specs32/specs_keys/gh80-3003-nicosmod/gh80-3003-nicosmod.kicad_sch

## KiCad design gh80-3003-nicosmod/gh80-3003-nicosmod.kicad_sch (2021-04-06)

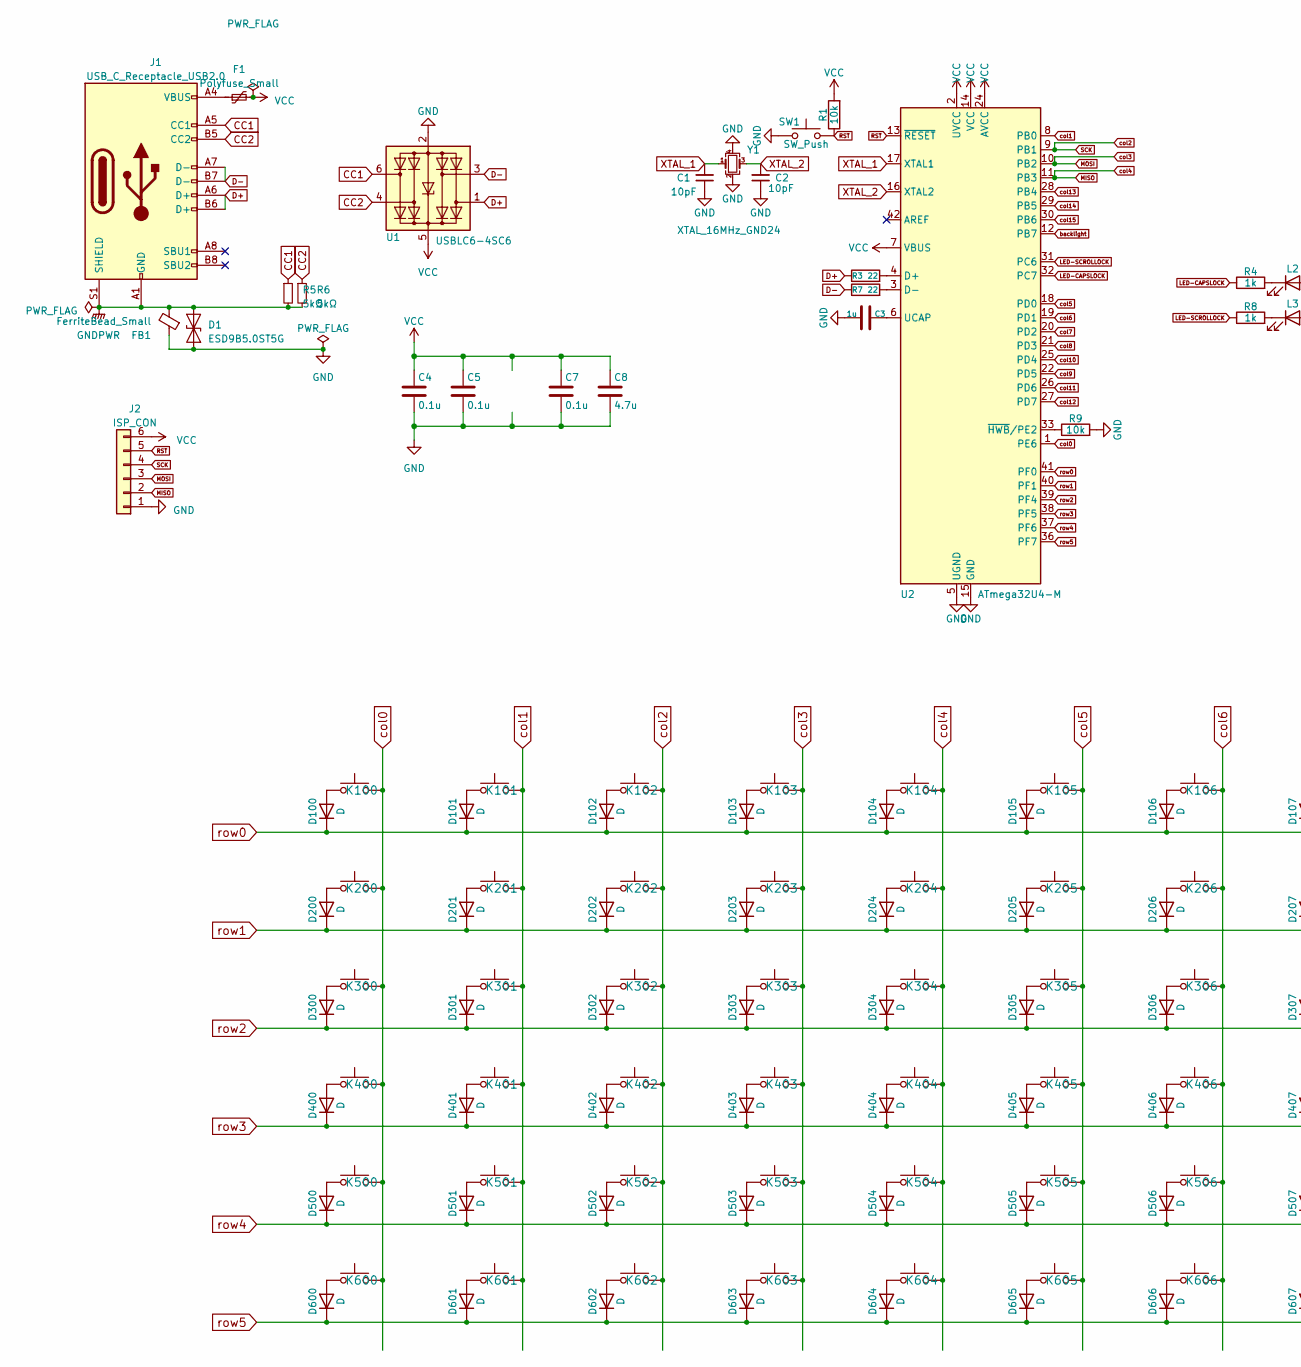
[picture p9: schematic gh80-3003-nicosmod.kicad_sch, part in row 1, column 1]

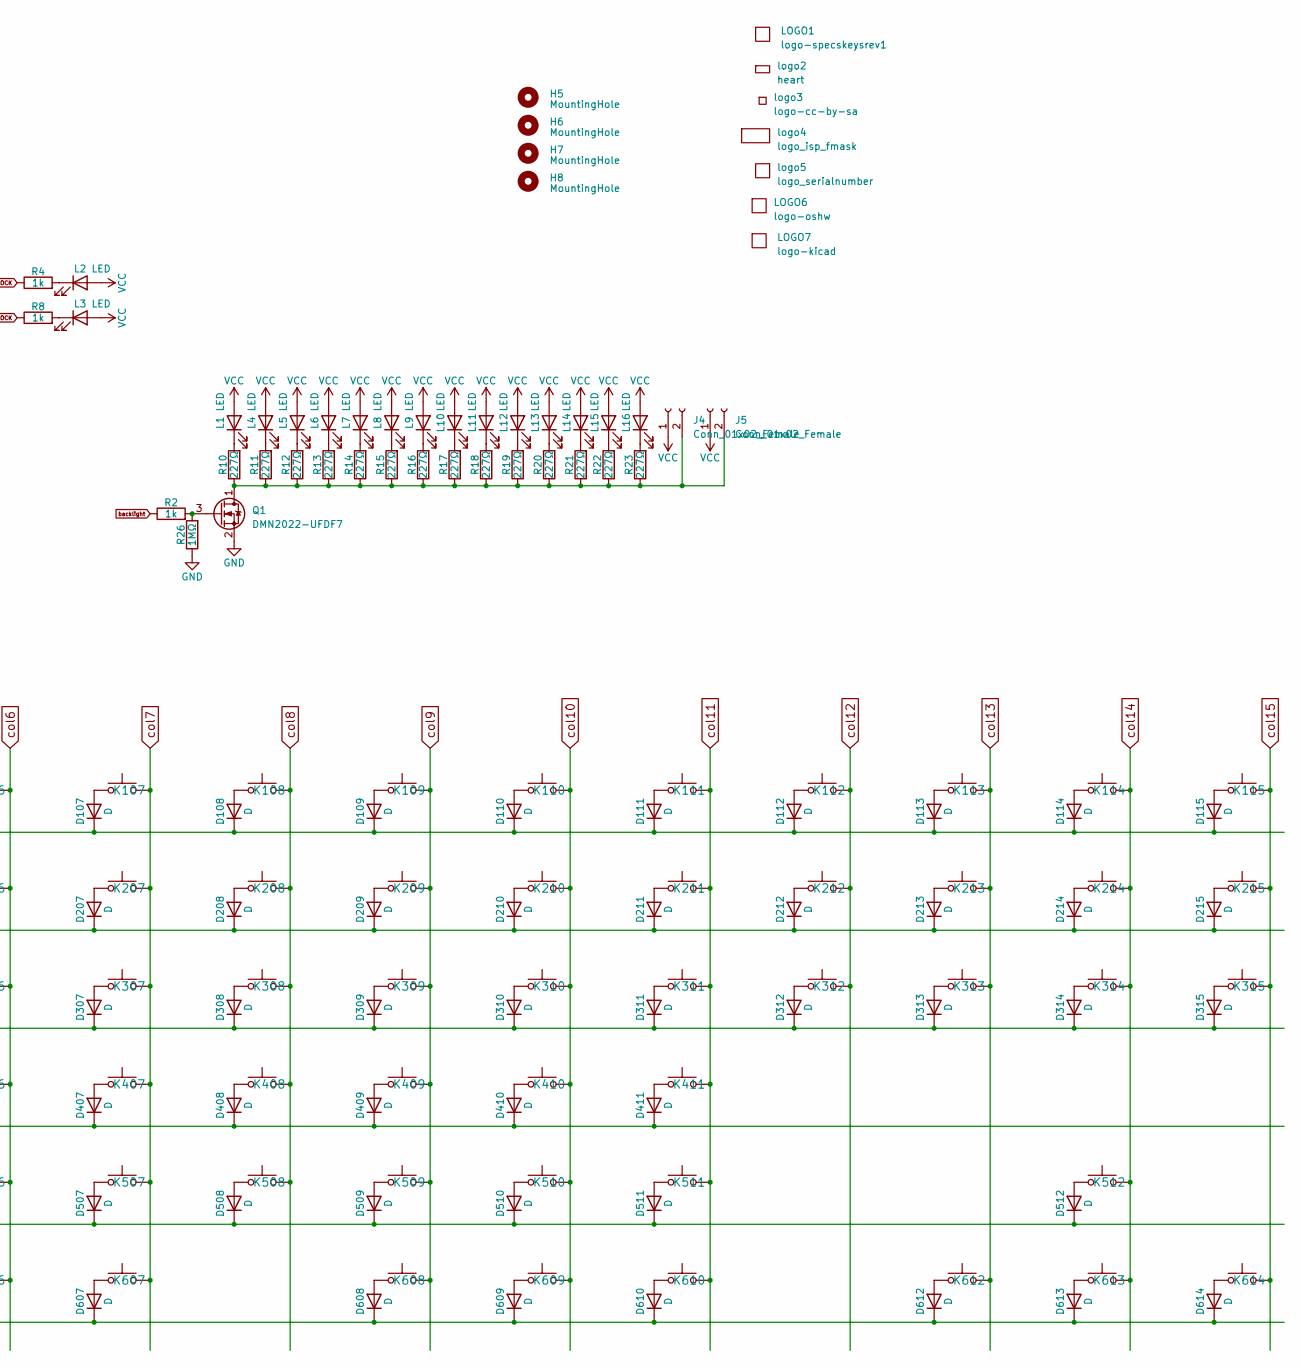
[picture p10: schematic gh80-3003-nicosmod.kicad_sch, part in row 1, column 2]

Parts:
C1, C2: 10pF; C_0603_1608Metric_Pad1.08x0.95mm_HandSolder
C3: 1u; C_0805_2012Metric_Pad1.18x1.45mm_HandSolder
C4, C5, C7: 0.1u; C_0603_1608Metric
C8: 4.7u; C_0805_2012Metric_Pad1.18x1.45mm_HandSolder
D1: ESD9B5.0ST5G; D_0402_1005Metric_Pad0.77x0.64mm_HandSolder
D100, D101, D102, D103, D104, D105, D106, D107, D108, D109, D110, D111, D112, D113, D114, D115, D200, D201, D202, D203, D204, D205, D206, D207, D208, D209, D210, D211, D212, D213, D214, D215, D300, D301, D302, D303, D304, D305, D306, D307, D308, D309, D310, D311, D312, D313, D314, D315, D400, D401, D402, D403, D404, D405, D406, D407, D408, D409, D410, D411, D500, D501, D502, D503, D504, D505, D506, D507, D508, D509, D510, D511, D512, D600, D601, D602, D603, D604, D605, D606, D607, D608, D609, D610, D612, D613, D614: D; D_0402_1005Metric_Pad0.77x0.64mm_HandSolder
F1: Polyfuse_Small; R_0805_2012Metric_Pad1.20x1.40mm_HandSolder
FB1: FerriteBead_Small; R_0805_2012Metric_Pad1.20x1.40mm_HandSolder
H5, H6, H7, H8: MountingHole; MountingHole_4mm
J1: USB_C_Receptacle_USB2.0; USB_C_Receptacle_JAE_DX07S016JA1R1500
J2: ISP_CON; Conn_01x06_SMD_2mm
J4, J5: Conn_01x02_Female; PinHeader_1x02_P2.00mm_Vertical
K100, K101, K102, K103, K104, K105, K106, K107, K108, K109, K110, K111, K112, K113, K114, K115, K200, K201, K202, K203, K204, K205, K206, K207, K208, K209, K210, K211, K213, K214, K215, K300, K301, K302, K303, K304, K305, K306, K307, K308, K309, K310, K311, K313, K314, K315, K400, K401, K402, K403, K404, K405, K406, K407, K408, K409, K410, K411, K500, K501, K502, K503, K504, K505, K506, K507, K508, K509, K510, K512, K600, K605, K609, K612, K613, K614: SW_Push; SW_Cherry_MX_1.00u_PCB
K212: SW_Push; SW_Cherry_MX_2.00u_PCB
K312: SW_Push; SW_Cherry_MX_ISOEnter_PCB
K511: SW_Push; SW_Cherry_MX_2.75u_PCB
K601, K604, K606, K608, K610: SW_Push; SW_Cherry_MX_1.50u_PCB
K602: SW_Push; SW_Cherry_MX_1.75u_PCB
K603: SW_Push; SW_Cherry_MX_1.25u_PCB
K607: SW_Push; SW_Cherry_MX_7.00u_PCB
L1, L2, L3, L4, L5, L6, L7, L8, L9, L10, L11, L12, L13, L14, L15, L16: LED; LED_0805_2012Metric_Pad1.15x1.40mm_HandSolder
LOGO1: logo-specskeysrev1; logo_specskeysrev1
LOGO6: logo-oshw; OSHW-Symbol_6.7x6mm_Copper
LOGO7: logo-kicad; KiCad-Logo2_5mm_Copper
Q1: DMN2022-UFDF7; U-DFN2020-6 (Type F)
R1, R9: 10k; R_0603_1608Metric
R2, R4, R8: 1k; R_0603_1608Metric
R3, R7: 22; R_0603_1608Metric
R5, R6: 5kΩ; R_0603_1608Metric
R10, R11, R12, R13, R14, R15, R16, R17, R18, R19, R20, R21, R22, R23: 227Ω; R_0805_2012Metric
R26: 1MΩ; R_0603_1608Metric
SW1: SW_Push; SW_SPST_TL3342
U1: USBLC6-4SC6; SOT-23-6
U2: ATmega32U4-M; QFN-44-1EP_7x7mm_P0.5mm_EP5.2x5.2mm_ThermalVias
Y1: XTAL_16MHz_GND24; Crystal_SMD_2016-4Pin_2.0x1.6mm
logo2: heart; logo_heart3
logo3: logo-cc-by-sa; cc-by-sa
logo4: logo_isp_fmask; ISP_AT32
logo5: logo_serialnumber; JLC-SERIAL

Connections:
CC1: J1.A5 (CC1), R5.1, U1.6 (I/O4)
CC2: J1.B5 (CC2), R6.1, U1.4 (I/O3)
D+: J1.A6 (D+), J1.B6 (D+), R3.1, U1.1 (I/O1)
D-: J1.A7 (D-), J1.B7 (D-), R7.1, U1.3 (I/O2)
GND: C1.1, C2.1, C3.2, C4.2, C5.2, C7.2, C8.2, D1.1 (A1), FB1.1, J2.1, Q1.2 (S), R9.2, R26.1, SW1.1, U1.2 (GND), U2.5 (UGND), U2.15 (GND), U2.23 (GND), U2.35 (GND), U2.43 (GND), U2.45 (GND), Y1.2, Y1.4
GNDPWR: D1.2 (A2), FB1.2, J1.A1 (GND), J1.A12 (GND), J1.B1 (GND), J1.B12 (GND), J1.S1 (SHIELD), R5.2, R6.2
LED-CAPSLOCK: R4.1, U2.32 (PC7)
LED-SCROLLOCK: R8.1, U2.31 (PC6)
unnamed: C3.1, U2.6 (UCAP)
unnamed: D100.2 (A), K100.2
unnamed: D101.2 (A), K101.2
unnamed: D102.2 (A), K102.2
unnamed: D103.2 (A), K103.2
unnamed: D104.2 (A), K104.2
unnamed: D105.2 (A), K105.2
unnamed: D106.2 (A), K106.2
unnamed: D107.2 (A), K107.2
unnamed: D108.2 (A), K108.2
unnamed: D109.2 (A), K109.2
unnamed: D110.2 (A), K110.2
unnamed: D111.2 (A), K111.2
unnamed: D112.2 (A), K112.2
unnamed: D113.2 (A), K113.2
unnamed: D114.2 (A), K114.2
unnamed: D115.2 (A), K115.2
unnamed: D200.2 (A), K200.2
unnamed: D201.2 (A), K201.2
unnamed: D202.2 (A), K202.2
unnamed: D203.2 (A), K203.2
unnamed: D204.2 (A), K204.2
unnamed: D205.2 (A), K205.2
unnamed: D206.2 (A), K206.2
unnamed: D207.2 (A), K207.2
unnamed: D208.2 (A), K208.2
unnamed: D209.2 (A), K209.2
unnamed: D210.2 (A), K210.2
unnamed: D211.2 (A), K211.2
unnamed: D212.2 (A), K212.2
unnamed: D213.2 (A), K213.2
unnamed: D214.2 (A), K214.2
unnamed: D215.2 (A), K215.2
unnamed: D300.2 (A), K300.2
unnamed: D301.2 (A), K301.2
unnamed: D302.2 (A), K302.2
unnamed: D303.2 (A), K303.2
unnamed: D304.2 (A), K304.2
unnamed: D305.2 (A), K305.2
unnamed: D306.2 (A), K306.2
unnamed: D307.2 (A), K307.2
unnamed: D308.2 (A), K308.2
unnamed: D309.2 (A), K309.2
unnamed: D310.2 (A), K310.2
unnamed: D311.2 (A), K311.2
unnamed: D312.2 (A), K312.2
unnamed: D313.2 (A), K313.2
unnamed: D314.2 (A), K314.2
unnamed: D315.2 (A), K315.2
unnamed: D400.2 (A), K400.2
unnamed: D401.2 (A), K401.2
unnamed: D402.2 (A), K402.2
unnamed: D403.2 (A), K403.2
unnamed: D404.2 (A), K404.2
unnamed: D405.2 (A), K405.2
unnamed: D406.2 (A), K406.2
unnamed: D407.2 (A), K407.2
unnamed: D408.2 (A), K408.2
unnamed: D409.2 (A), K409.2
unnamed: D410.2 (A), K410.2
unnamed: D411.2 (A), K411.2
unnamed: D500.2 (A), K500.2
unnamed: D501.2 (A), K501.2
unnamed: D502.2 (A), K502.2
unnamed: D503.2 (A), K503.2
unnamed: D504.2 (A), K504.2
unnamed: D505.2 (A), K505.2
unnamed: D506.2 (A), K506.2
unnamed: D507.2 (A), K507.2
unnamed: D508.2 (A), K508.2
unnamed: D509.2 (A), K509.2
unnamed: D510.2 (A), K510.2
unnamed: D511.2 (A), K511.2
unnamed: D512.2 (A), K512.2
unnamed: D600.2 (A), K600.2
unnamed: D601.2 (A), K601.2
unnamed: D602.2 (A), K602.2
unnamed: D603.2 (A), K603.2
unnamed: D604.2 (A), K604.2
unnamed: D605.2 (A), K605.2
unnamed: D606.2 (A), K606.2
unnamed: D607.2 (A), K607.2
unnamed: D608.2 (A), K608.2
unnamed: D609.2 (A), K609.2
unnamed: D610.2 (A), K610.2
unnamed: D612.2 (A), K612.2
unnamed: D613.2 (A), K613.2
unnamed: D614.2 (A), K614.2
unnamed: F1.1, J1.A4 (VBUS), J1.A9 (VBUS), J1.B4 (VBUS), J1.B9 (VBUS)
unnamed: J4.2, J5.2, Q1.1 (D), R10.1, R11.1, R12.1, R13.1, R14.1, R15.1, R16.1, R17.1, R18.1, R19.1, R20.1, R21.1, R22.1, R23.1
unnamed: L1.1 (K), R10.2
unnamed: L2.1 (K), R4.2
unnamed: L3.1 (K), R8.2
unnamed: L4.1 (K), R11.2
unnamed: L5.1 (K), R12.2
unnamed: L6.1 (K), R13.2
unnamed: L7.1 (K), R14.2
unnamed: L8.1 (K), R15.2
unnamed: L9.1 (K), R16.2
unnamed: L10.1 (K), R17.2
unnamed: L11.1 (K), R18.2
unnamed: L12.1 (K), R19.2
unnamed: L13.1 (K), R20.2
unnamed: L14.1 (K), R21.2
unnamed: L15.1 (K), R22.2
unnamed: L16.1 (K), R23.2
unnamed: Q1.3 (G), R2.2, R26.2
unnamed: R3.2, U2.4 (D+)
unnamed: R7.2, U2.3 (D-)
unnamed: R9.1, U2.33 (~HWB~/PE2)
RST: J2.5, R1.1, SW1.2, U2.13 (~RESET)
VCC: C4.1, C5.1, C7.1, C8.1, F1.2, J2.6, J4.1, J5.1, L1.2 (A), L2.2 (A), L3.2 (A), L4.2 (A), L5.2 (A), L6.2 (A), L7.2 (A), L8.2 (A), L9.2 (A), L10.2 (A), L11.2 (A), L12.2 (A), L13.2 (A), L14.2 (A), L15.2 (A), L16.2 (A), R1.2, U1.5 (VBUS), U2.2 (UVCC), U2.7 (VBUS), U2.14 (VCC), U2.24 (AVCC), U2.34 (VCC), U2.44 (AVCC)
XTAL_1: C1.2, U2.17 (XTAL1), Y1.1
XTAL_2: C2.2, U2.16 (XTAL2), Y1.3
backlight: R2.1, U2.12 (PB7)
col0: K100.1, K200.1, K300.1, K400.1, K500.1, K600.1, U2.1 (PE6)
col1: K101.1, K201.1, K301.1, K401.1, K501.1, K601.1, U2.8 (PB0)
col2: J2.4, K102.1, K202.1, K302.1, K402.1, K502.1, K602.1, U2.9 (PB1)
col3: J2.3, K103.1, K203.1, K303.1, K403.1, K503.1, K603.1, U2.10 (PB2)
col4: J2.2, K104.1, K204.1, K304.1, K404.1, K504.1, K604.1, U2.11 (PB3)
col5: K105.1, K205.1, K305.1, K405.1, K505.1, K605.1, U2.18 (PD0)
col6: K106.1, K206.1, K306.1, K406.1, K506.1, K606.1, U2.19 (PD1)
col7: K107.1, K207.1, K307.1, K407.1, K507.1, K607.1, U2.20 (PD2)
col8: K108.1, K208.1, K308.1, K408.1, K508.1, U2.21 (PD3)
col9: K109.1, K209.1, K309.1, K409.1, K509.1, K608.1, U2.22 (PD5)
col10: K110.1, K210.1, K310.1, K410.1, K510.1, K609.1, U2.25 (PD4)
col11: K111.1, K211.1, K311.1, K411.1, K511.1, K610.1, U2.26 (PD6)
col12: K112.1, K212.1, K312.1, U2.27 (PD7)
col13: K113.1, K213.1, K313.1, K612.1, U2.28 (PB4)
col14: K114.1, K214.1, K314.1, K512.1, K613.1, U2.29 (PB5)
col15: K115.1, K215.1, K315.1, K614.1, U2.30 (PB6)
row0: D100.1 (K), D101.1 (K), D102.1 (K), D103.1 (K), D104.1 (K), D105.1 (K), D106.1 (K), D107.1 (K), D108.1 (K), D109.1 (K), D110.1 (K), D111.1 (K), D112.1 (K), D113.1 (K), D114.1 (K), D115.1 (K), U2.41 (PF0)
row1: D200.1 (K), D201.1 (K), D202.1 (K), D203.1 (K), D204.1 (K), D205.1 (K), D206.1 (K), D207.1 (K), D208.1 (K), D209.1 (K), D210.1 (K), D211.1 (K), D212.1 (K), D213.1 (K), D214.1 (K), D215.1 (K), U2.40 (PF1)
row2: D300.1 (K), D301.1 (K), D302.1 (K), D303.1 (K), D304.1 (K), D305.1 (K), D306.1 (K), D307.1 (K), D308.1 (K), D309.1 (K), D310.1 (K), D311.1 (K), D312.1 (K), D313.1 (K), D314.1 (K), D315.1 (K), U2.39 (PF4)
row3: D400.1 (K), D401.1 (K), D402.1 (K), D403.1 (K), D404.1 (K), D405.1 (K), D406.1 (K), D407.1 (K), D408.1 (K), D409.1 (K), D410.1 (K), D411.1 (K), U2.38 (PF5)
row4: D500.1 (K), D501.1 (K), D502.1 (K), D503.1 (K), D504.1 (K), D505.1 (K), D506.1 (K), D507.1 (K), D508.1 (K), D509.1 (K), D510.1 (K), D511.1 (K), D512.1 (K), U2.37 (PF6)
row5: D600.1 (K), D601.1 (K), D602.1 (K), D603.1 (K), D604.1 (K), D605.1 (K), D606.1 (K), D607.1 (K), D608.1 (K), D609.1 (K), D610.1 (K), D612.1 (K), D613.1 (K), D614.1 (K), U2.36 (PF7)
